ZIOCC/Zio-Qwiic-PM2.5-Air-Quality-Sensor-Adapter-Board/micropython/ssd1327.py

# MicroPython SSD1327 OLED driver, I2C interface

# fork into two drivers, one with and without framebuf
# Rewrite by mcauser, https://github.com/mcauser/micropython-ssd1327
# Collected by Alex Chu, https://github.com/ZIOCC/Zio-Qwiic-OLED-Display-1.5inch-128x128/blob/master/micropython/ssd1327.py

#
from micropython import const
import time
import framebuf


# commands
SET_COL_ADDR          = const(0x15)
SET_SCROLL_DEACTIVATE = const(0x2E)
SET_ROW_ADDR          = const(0x75)
SET_CONTRAST          = const(0x81)
SET_SEG_REMAP         = const(0xA0)
SET_DISP_START_LINE   = const(0xA1)
SET_DISP_OFFSET       = const(0xA2)
SET_DISP_MODE         = const(0xA4) # 0xA4 normal, 0xA5 all on, 0xA6 all off, 0xA7 when inverted
SET_MUX_RATIO         = const(0xA8)
SET_FN_SELECT_A       = const(0xAB)
SET_DISP              = const(0xAE) # 0xAE power off, 0xAF power on
SET_PHASE_LEN         = const(0xB1)
SET_DISP_CLK_DIV      = const(0xB3)
SET_SECOND_PRECHARGE  = const(0xB6)
SET_GRAYSCALE_TABLE   = const(0xB8)
SET_GRAYSCALE_LINEAR  = const(0xB9)
SET_PRECHARGE         = const(0xBC)
SET_VCOM_DESEL        = const(0xBE)
SET_FN_SELECT_B       = const(0xD5)
SET_COMMAND_LOCK      = const(0xFD)

# registers
REG_CMD  = const(0x80)
REG_DATA = const(0x40)


class SSD1327:
    def __init__(self, width, height, external_vcc):
        self.width = width
        self.height = height
        self.external_vcc = external_vcc
        self.buffer = bytearray(self.width * self.height // 2)
        self.framebuf = framebuf.FrameBuffer(self.buffer, self.width, self.height, framebuf.GS4_HMSB)
        self.poweron()
        self.init_display()

    def init_display(self):
        for cmd in (
            SET_COMMAND_LOCK, 0x12, # Unlock
            SET_DISP, # Display off
            # Resolution and layout
            SET_DISP_START_LINE, 0x00,
            SET_DISP_OFFSET, 0x20, # Set vertical offset by COM from 0~127
            # Set re-map
            # Enable column address re-map
            # Disable nibble re-map
            # Horizontal address increment
            # Enable COM re-map
            # Enable COM split odd even
            SET_SEG_REMAP, 0x51,
            SET_MUX_RATIO, self.height - 1,
            # Timing and driving scheme
            SET_FN_SELECT_A, 0x01, # Enable internal VDD regulator
            SET_PHASE_LEN, 0x51, # Phase 1: 1 DCLK, Phase 2: 5 DCLKs
            SET_DISP_CLK_DIV, 0x01, # Divide ratio: 1, Oscillator Frequency: 0
            SET_PRECHARGE, 0x08, # Set pre-charge voltage level: VCOMH
            SET_VCOM_DESEL, 0x07, # Set VCOMH COM deselect voltage level: 0.86*Vcc
            SET_SECOND_PRECHARGE, 0x01, # Second Pre-charge period: 1 DCLK
            SET_FN_SELECT_B, 0x62, # Enable enternal VSL, Enable second precharge
            # Display
            SET_GRAYSCALE_LINEAR, # Use linear greyscale lookup table
            SET_CONTRAST, 0x7f, # Medium brightness
            SET_DISP_MODE, # Normal, not inverted
            # 96x96:
            # SET_ROW_ADDR, 0 95,
            # SET_COL_ADDR, 8, 55,
            # 128x128:
            # SET_ROW_ADDR, 0 127,
            # SET_COL_ADDR, 0, 63,
            SET_ROW_ADDR, 0x00, self.height - 1,
            SET_COL_ADDR, ((128 - self.width) // 4), 63 - ((128 - self.width) // 4),

            SET_SCROLL_DEACTIVATE,
            SET_DISP | 0x01): # Display on
            self.write_cmd(cmd)
        self.fill(0)
        self.show()

    def poweroff(self):
        self.write_cmd(SET_FN_SELECT_A)
        self.write_cmd(0x00) # Disable internal VDD regulator, to save power
        self.write_cmd(SET_DISP)

    def poweron(self):
        self.write_cmd(SET_FN_SELECT_A)
        self.write_cmd(0x01) # Enable internal VDD regulator
        self.write_cmd(SET_DISP | 0x01)

    def contrast(self, contrast):
        self.write_cmd(SET_CONTRAST)
        self.write_cmd(contrast) # 0-255

    def invert(self, invert):
        self.write_cmd(SET_DISP_MODE | (invert & 1) << 1 | (invert & 1)) # 0xA4=Normal, 0xA7=Inverted

    def show(self):
        self.write_cmd(SET_COL_ADDR)
        self.write_cmd((128 - self.width) // 4)
        self.write_cmd(63 - ((128 - self.width) // 4))
        self.write_cmd(SET_ROW_ADDR)
        self.write_cmd(0x00)
        self.write_cmd(self.height - 1)
        self.write_data(self.buffer)

    def fill(self, col):
        self.framebuf.fill(col)

    def pixel(self, x, y, col):
        self.framebuf.pixel(x, y, col)

    def scroll(self, dx, dy):
        self.framebuf.scroll(dx, dy)
        # software scroll

    def text(self, string, x, y, col=15):
        self.framebuf.text(string, x, y, col)


class SSD1327_I2C(SSD1327):
    def __init__(self, width, height, i2c, addr=0x3c, external_vcc=False):
        self.i2c = i2c
        self.addr = addr
        self.temp = bytearray(2)
        super().__init__(width, height, external_vcc)

    def write_cmd(self, cmd):
        self.temp[0] = REG_CMD # Co=1, D/C#=0
        self.temp[1] = cmd
        self.i2c.writeto(self.addr, self.temp)

    def write_data(self, buf):
        self.temp[0] = self.addr << 1
        self.temp[1] = REG_DATA # Co=0, D/C#=1
        self.i2c.start()
        self.i2c.write(self.temp)
        self.i2c.write(buf)
        self.i2c.stop()


class QWIIC_128X128_OLED(SSD1327_I2C):
    def __init__(self, i2c):
        super().__init__(128, 128, i2c)
        self.changesetting()

    def changesetting(self):
        # Unlock
        self.write_cmd(0xFD)
        self.write_cmd(0x12)
        #
        # # Display off
        # display.write_cmd(0xAE)

        # Set column address 0-127
        self.write_cmd(0x15)
        self.write_cmd(0x00)  # was 0x08 on 96x96 ((128-width)/depth)=8
        self.write_cmd(0x7F)  # was 0x37 on 96x96 (63-((128-width)/depth))=55

        # Set row address 0-127
        self.write_cmd(0x75)
        self.write_cmd(0x00)
        self.write_cmd(0x7F)  # was 0x5F on 96x96 (height-1=95)

        # Set start line = 0
        self.write_cmd(0xA1)
        self.write_cmd(0x00)

        # Display offset = 0
        self.write_cmd(0xA2)
        self.write_cmd(0x00)  # was 0x20 on 96x96 (128-height=32)

        # Display normal
        self.write_cmd(0xA4)

        # Set multiplex ratio
        self.write_cmd(0xA8)
        self.write_cmd(0x7F)  # was 0x5F on 96x96 (height-1=95)
